Wassasin/leddimmer/fw/main/drivers.h

#pragma once

#include <esp_err.h>

#define DRIVER_PWM_MAX 2047
#define DRIVERS_COUNT 2

typedef uint16_t driver_pwm11_t;
typedef driver_pwm11_t drivers_pwm11_t[DRIVERS_COUNT];

esp_err_t drivers_init(void);

esp_err_t drivers_command(uint8_t driver_i, const driver_pwm11_t duty);
void drivers_fetch(drivers_pwm11_t* duty_out);

void drivers_update(void);
