Wassasin/leddimmer/fw/main/led.c

#include "led.h"

#include <driver/rmt_tx.h>
#include <esp_log.h>
#include <freertos/FreeRTOS.h>
#include <freertos/semphr.h>
#include <string.h>

#include "util/led_strip_encoder.h"

#define TAG "led"

#define RMT_LED_STRIP_RESOLUTION_HZ 10000000 // 10MHz resolution, 1 tick = 0.1us (led strip needs a high resolution)
#define RMT_LED_STRIP_GPIO_NUM 10
#define LED_NUMBERS 1

static SemaphoreHandle_t s_mutex;
static rgb_t m_current_rgb;
static uint8_t m_led_strip_pixels[LED_NUMBERS * 3];

static rmt_channel_handle_t m_led_chan = NULL;
static rmt_encoder_handle_t m_led_encoder = NULL;

static void led_set_color_unsafe(rgb_t rgb)
{
    m_led_strip_pixels[0] = rgb.g;
    m_led_strip_pixels[1] = rgb.r;
    m_led_strip_pixels[2] = rgb.b;

    rmt_transmit_config_t tx_config = {
        .loop_count = 0, // no transfer loop
    };

    ESP_ERROR_CHECK(rmt_transmit(m_led_chan, m_led_encoder, m_led_strip_pixels, sizeof(m_led_strip_pixels), &tx_config));
    ESP_ERROR_CHECK(rmt_tx_wait_all_done(m_led_chan, portMAX_DELAY));

    // The LED array has a wait period at the end.
    vTaskDelay(pdMS_TO_TICKS(10));
}

esp_err_t led_init(void)
{
    s_mutex = xSemaphoreCreateMutex();

    rmt_tx_channel_config_t tx_chan_config = {
        .clk_src = RMT_CLK_SRC_DEFAULT, // select source clock
        .gpio_num = RMT_LED_STRIP_GPIO_NUM,
        .mem_block_symbols = 64, // increase the block size can make the LED less flickering
        .resolution_hz = RMT_LED_STRIP_RESOLUTION_HZ,
        .trans_queue_depth = 4, // set the number of transactions that can be pending in the background
    };
    ESP_ERROR_CHECK(rmt_new_tx_channel(&tx_chan_config, &m_led_chan));

    led_strip_encoder_config_t encoder_config = {
        .resolution = RMT_LED_STRIP_RESOLUTION_HZ,
    };
    ESP_ERROR_CHECK(rmt_new_led_strip_encoder(&encoder_config, &m_led_encoder));

    ESP_ERROR_CHECK(rmt_enable(m_led_chan));

    led_set_color_unsafe((rgb_t) { .r = 0x00, .g = 0x00, .b = 0x00 });

    return ESP_OK;
}

static bool rgb_eq(rgb_t x, rgb_t y)
{
    return memcmp(x.buf, y.buf, sizeof(x.buf)) == 0;
}

void led_set_color(rgb_t rgb)
{
    xSemaphoreTake(s_mutex, portMAX_DELAY);
    if (!rgb_eq(rgb, m_current_rgb)) {
        memcpy(m_current_rgb.buf, rgb.buf, sizeof(rgb.buf));
        led_set_color_unsafe(rgb);
    }
    xSemaphoreGive(s_mutex);
}
