Wassasin/leddimmer/fw/main/wifi.c

#include "wifi.h"

#include <driver/gpio.h>
#include <esp_event.h>
#include <esp_log.h>
#include <esp_netif.h>
#include <esp_wifi.h>
#include <lwip/apps/netbiosns.h>

#include "events.h"

#define TAG "wifi"

#define DNS_HOST_NAME "leddimmer"

#define DEFAULT_LISTEN_INTERVAL 3
#define DEFAULT_BEACON_TIMEOUT 100
#define DEFAULT_PS_MODE WIFI_PS_NONE

static void event_handler(void* arg, esp_event_base_t event_base,
    int32_t event_id, void* event_data)
{
    if (event_base == WIFI_EVENT && event_id == WIFI_EVENT_STA_START) {
        esp_wifi_connect();
    } else if (event_base == WIFI_EVENT && event_id == WIFI_EVENT_STA_DISCONNECTED) {
        esp_wifi_connect();

        ESP_ERROR_CHECK(esp_event_post(EVENTS, EVENT_OFFLINE,
            NULL, 0, portMAX_DELAY));
    } else if (event_base == IP_EVENT && event_id == IP_EVENT_STA_GOT_IP) {
        ip_event_got_ip_t* event = (ip_event_got_ip_t*)event_data;
        const esp_netif_ip_info_t* ip_info = &event->ip_info;

        ESP_LOGI(TAG, "ETHIP:" IPSTR, IP2STR(&ip_info->ip));
        ESP_LOGI(TAG, "ETHMASK:" IPSTR, IP2STR(&ip_info->netmask));
        ESP_LOGI(TAG, "ETHGW:" IPSTR, IP2STR(&ip_info->gw));

        ESP_ERROR_CHECK(esp_event_post(EVENTS, EVENT_ONLINE,
            NULL, 0, portMAX_DELAY));
    }
}

esp_err_t wifi_init(void)
{
    ESP_ERROR_CHECK(esp_netif_init());

    netbiosns_init();
    netbiosns_set_name(DNS_HOST_NAME);

    esp_netif_t* sta_netif = esp_netif_create_default_wifi_sta();
    assert(sta_netif);

    wifi_init_config_t cfg = WIFI_INIT_CONFIG_DEFAULT();
    ESP_ERROR_CHECK(esp_wifi_init(&cfg));

    ESP_ERROR_CHECK(esp_event_handler_instance_register(WIFI_EVENT, ESP_EVENT_ANY_ID, &event_handler, NULL, NULL));
    ESP_ERROR_CHECK(esp_event_handler_instance_register(IP_EVENT, IP_EVENT_STA_GOT_IP, &event_handler, NULL, NULL));

    wifi_config_t wifi_config = {
        .sta = {
            .ssid = CONFIG_WIFI_SSID,
            .password = CONFIG_WIFI_PASSPHRASE,
            .listen_interval = DEFAULT_LISTEN_INTERVAL,
        },
    };
    ESP_ERROR_CHECK(esp_wifi_set_mode(WIFI_MODE_STA));
    ESP_ERROR_CHECK(esp_wifi_set_config(WIFI_IF_STA, &wifi_config));
    ESP_ERROR_CHECK(esp_wifi_start());
    ESP_ERROR_CHECK(esp_wifi_set_inactive_time(WIFI_IF_STA, DEFAULT_BEACON_TIMEOUT));

    esp_wifi_set_ps(DEFAULT_PS_MODE);

    return ESP_OK;
}
